yuikosakuma/IoTLiteracyEdu/material/processing/servo_interface/data/servo_bg.png

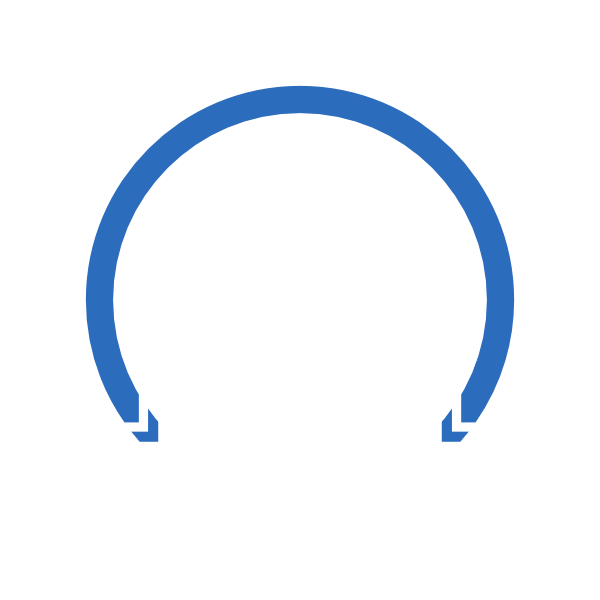
material/processing/servo_interface/data/servo_bg.png
