yuikosakuma/IoTLiteracyEdu/material/processing/secondWindow/secondApplet.pde

class SecondApplet extends PApplet {
  PApplet parent;
  
  SecondApplet(PApplet _parent) {
    super();
    // set parent
    this.parent = _parent;
    //// init window
    try {
      java.lang.reflect.Method handleSettingsMethod =
        this.getClass().getSuperclass().getDeclaredMethod("handleSettings", null);
      handleSettingsMethod.setAccessible(true);
      handleSettingsMethod.invoke(this, null);
    } catch (Exception ex) {
      ex.printStackTrace();
    }
    
    PSurface surface = super.initSurface();
    surface.placeWindow(new int[]{0, 0}, new int[]{0, 0});
    
    this.showSurface();
    this.startSurface();
  }
  
  void settings() {
    size(300, 300);
  }
  
  void setup() {
  }
  
  void draw() {
    background(frameCount % 255);
    fill(0);
    ellipse(width/2, height/2, width/2, height/2);
  }
}
